eilidh-h/nuclear_reactor_simulator/Current Design Files/Circuitry Files/Gerber and Layout Files/PCB Bar Graph PCB 3D.png

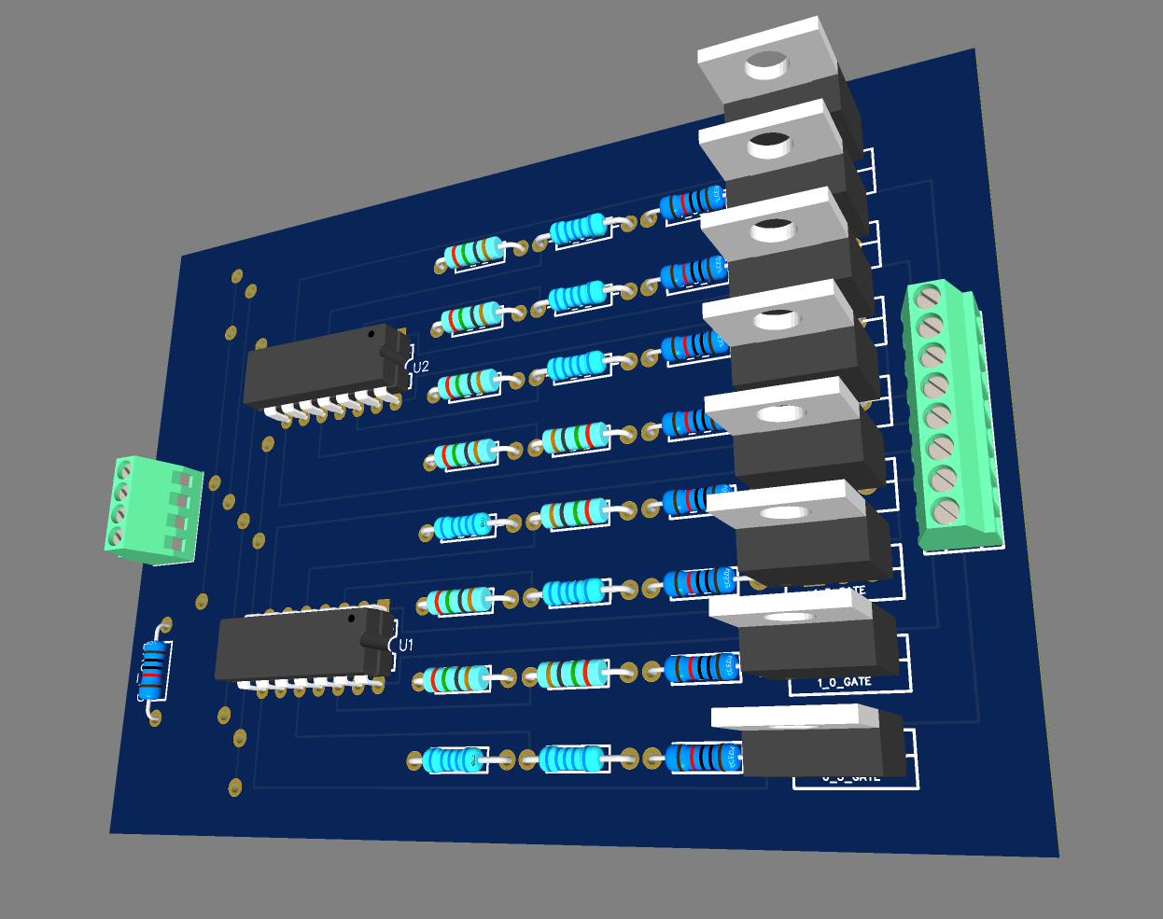
Current Design Files/Circuitry Files/Gerber and Layout Files/PCB Bar Graph PCB 3D.png
