eilidh-h/nuclear_reactor_simulator/Current Design Files/Datasheets/Momentary Switches - No Datasheet Available.png

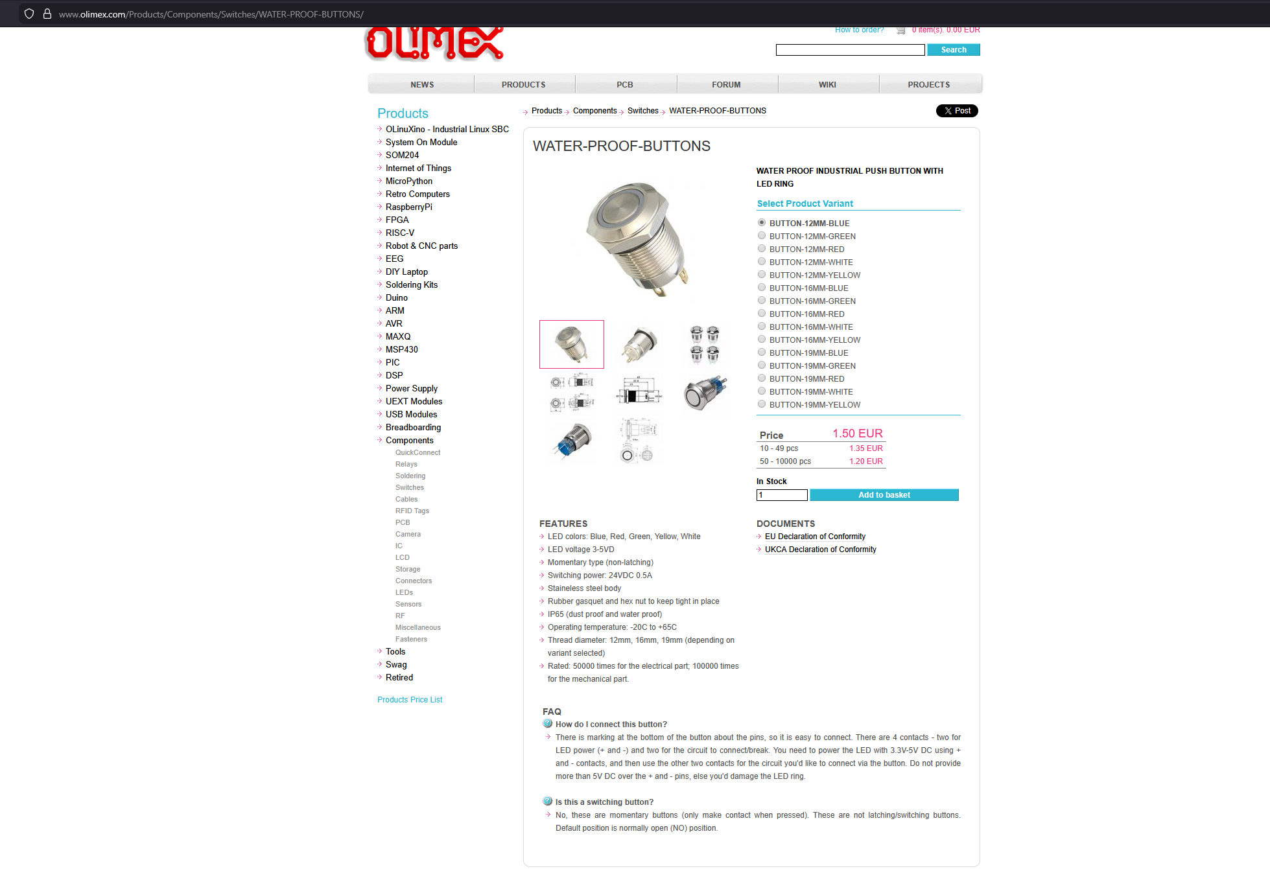
Current Design Files/Datasheets/Momentary Switches - No Datasheet Available.png
