eilidh-h/nuclear_reactor_simulator/Current Design Files/Case Files/Part & Assembly Files/SIM_WING_RIGHT_001.SLDPRT

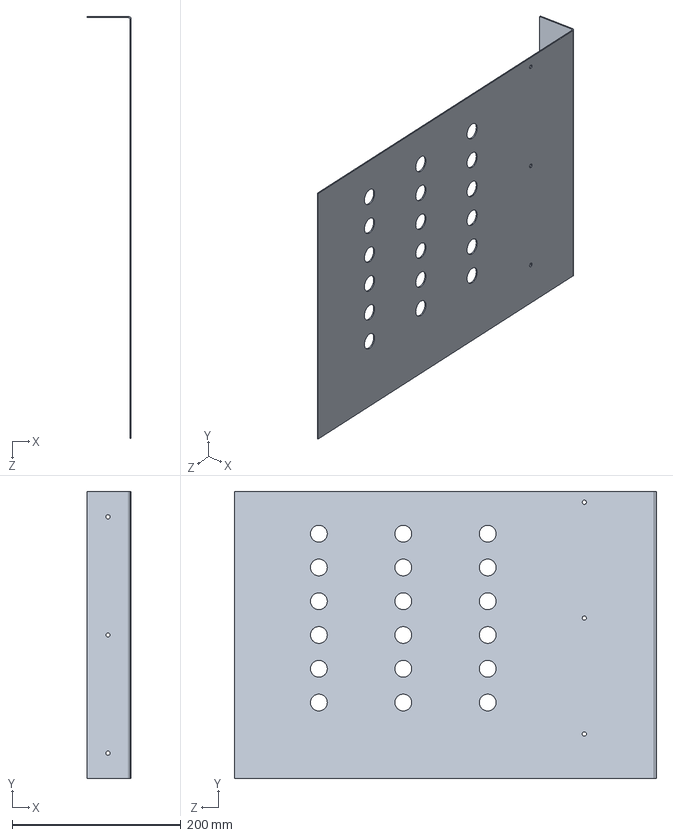
[picture p25: CAD file, 2026-07-31]
Current Design Files/Case Files/Part & Assembly Files/SIM_WING_RIGHT_001.SLDPRT
52.5 x 340.0 x 500.0 mm
