eilidh-h/nuclear_reactor_simulator/Current Design Files/Case Files/Part & Assembly Files/SIM_BASE_001.SLDPRT

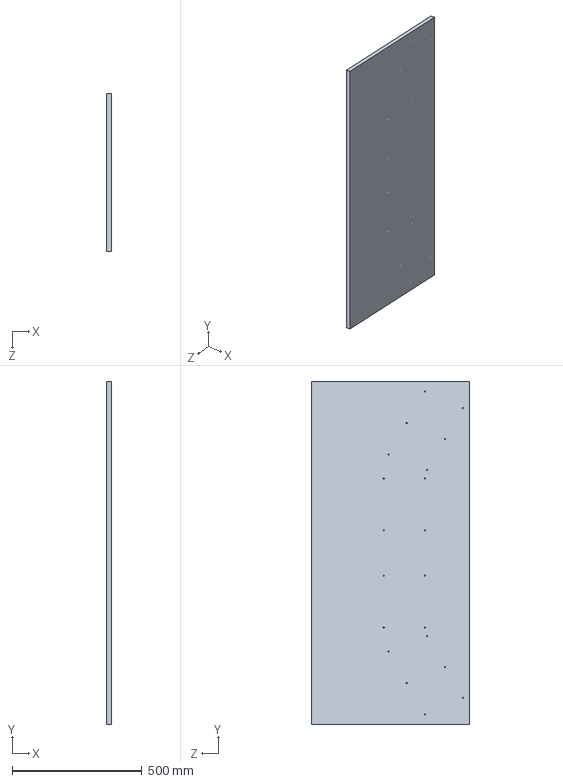
[picture p26: CAD file, 2026-07-31]
Current Design Files/Case Files/Part & Assembly Files/SIM_BASE_001.SLDPRT
19.1 x 1321.0 x 610.0 mm
