eilidh-h/nuclear_reactor_simulator/Current Design Files/Case Files/Part & Assembly Files/SIM_OVERVIEW_001_002.SLDASM

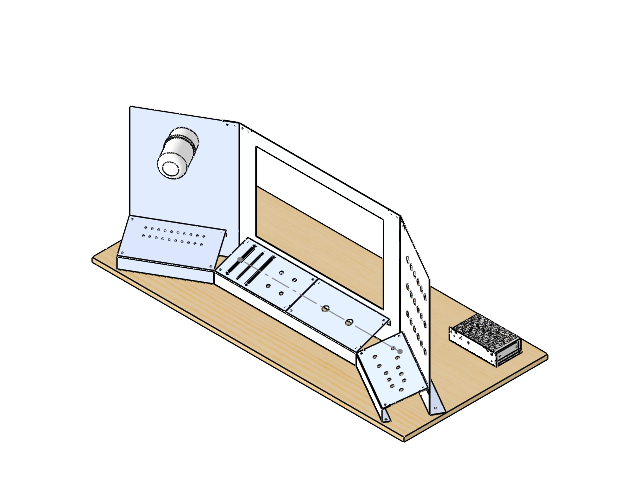
[picture p27: CAD file, 2026-07-31]
Current Design Files/Case Files/Part & Assembly Files/SIM_OVERVIEW_001_002.SLDASM
Back Panel Main
Reactor Control
SCRAM Panel
control panel prop
Wing Right
Wing Left
control panel prop - wings x 2
alarm light panel
Simulation Control
control panel top mount
ptb0143-2010bp.stp x 2
control panel top mount - wings x 2
alarm beacon
Simulator Wood Base
906-D-0_1.stp
NUT_1.stp
NUT_CPY_1.stp
NUT_CPY1_1.stp
NUT_CPY2_1.stp
NUT_CPY3_1.stp
NU_1.stp
NU_CPY_1.stp
NU_CPY1_1.stp
ADD-155-pcb_1.stp
ADD-155-T_1.stp
TB_1.stp
Angle Bracket x 2
